acornelissen/Infidex_176_v_IDENTIDEM_design_remix/flocking/dxf/chamber-bottom.dxf

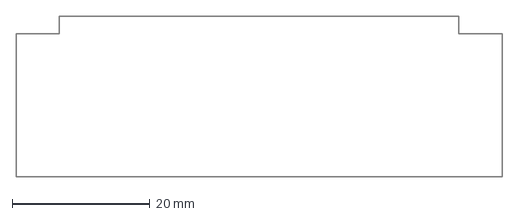
[picture p26: CAD file, 2026-09-22]
flocking/dxf/chamber-bottom.dxf
70.6 x 23.3 mm
