acornelissen/Infidex_176_v_IDENTIDEM_design_remix/3mf/parts/drag-cover.3mf

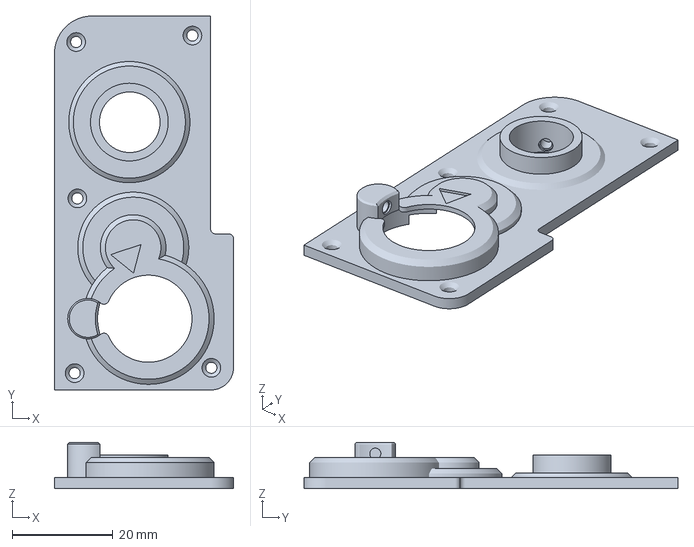
[picture p27: CAD file, 2026-09-30]
3mf/parts/drag-cover.3mf
35.5 x 74.1 x 9.20 mm
