acornelissen/Infidex_176_v_IDENTIDEM_design_remix/3mf/parts/advance-knob.3mf

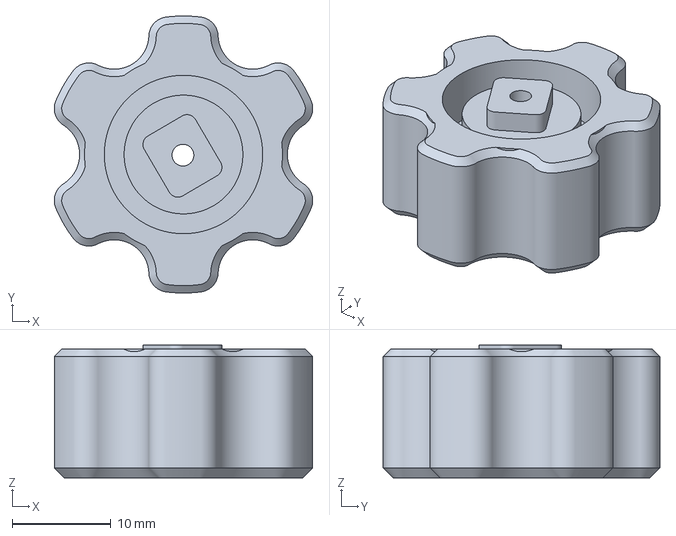
[picture p28: CAD file, 2026-09-28]
3mf/parts/advance-knob.3mf
26.1 x 28.0 x 13.4 mm
