acornelissen/Infidex_176_v_IDENTIDEM_design_remix/3mf/parts/rewind-knob.3mf

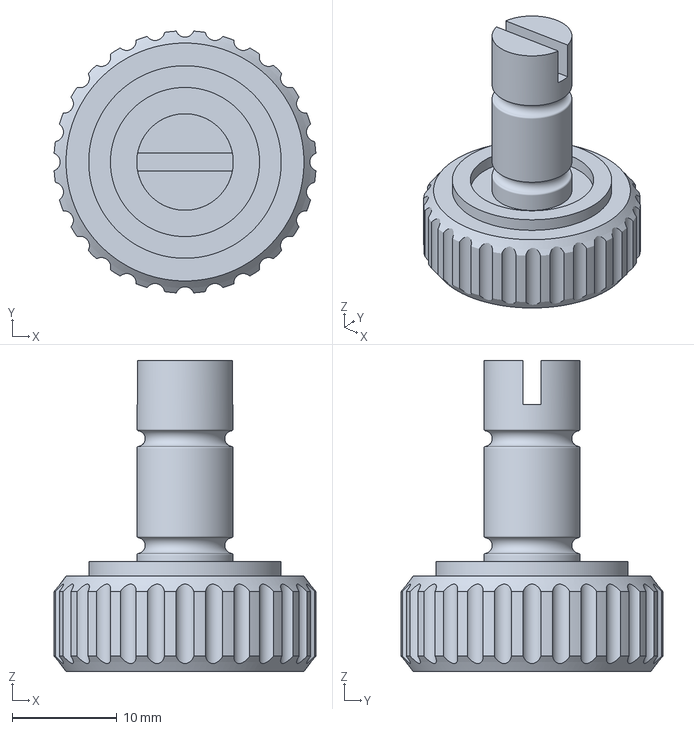
[picture p29: CAD file, 2026-09-28]
3mf/parts/rewind-knob.3mf
25.0 x 25.0 x 29.7 mm
