acornelissen/Infidex_176_v_IDENTIDEM_design_remix/3mf/parts/simple-cover.3mf

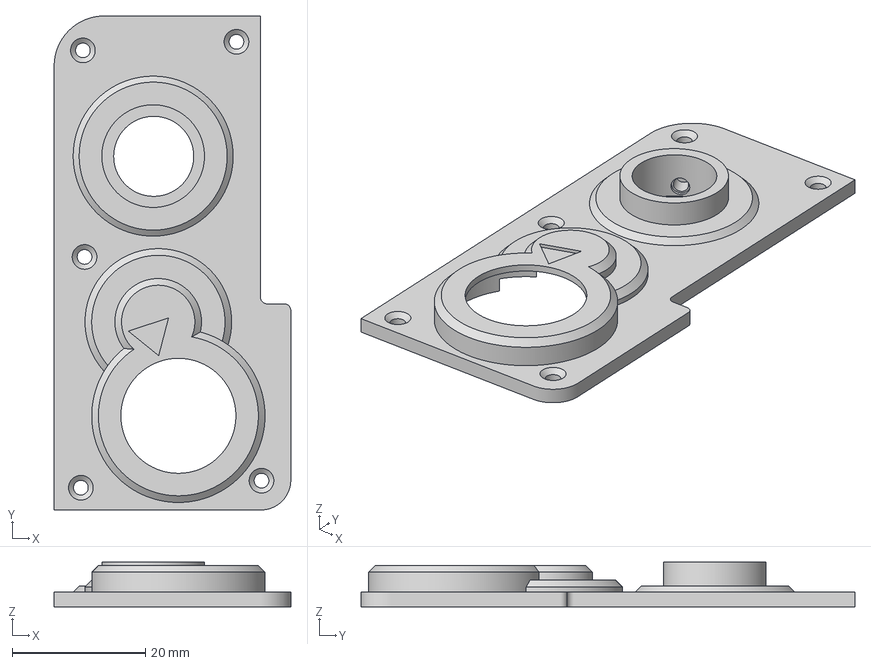
[picture p30: CAD file, 2026-09-28]
3mf/parts/simple-cover.3mf
35.5 x 74.1 x 6.70 mm
