acornelissen/Infidex_176_v_IDENTIDEM_design_remix/3mf/parts/counter-idler-1.3mf

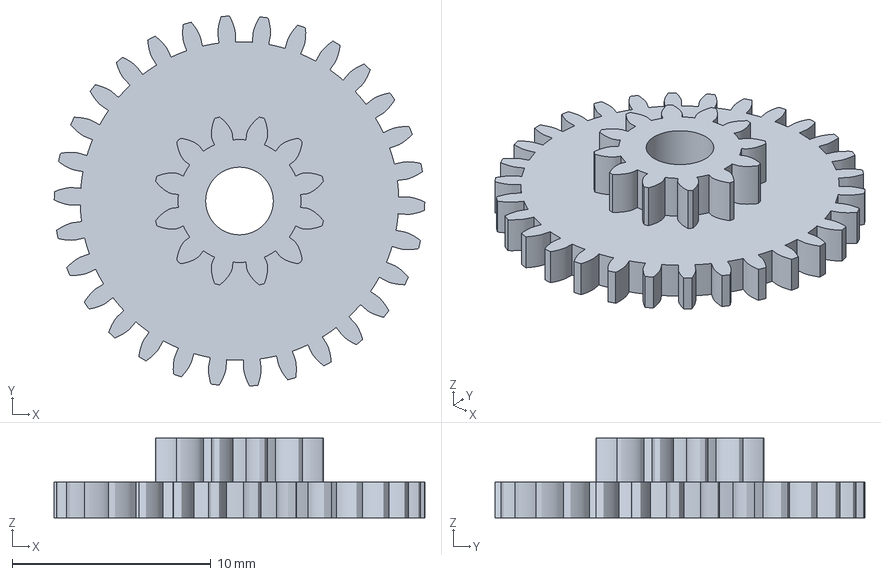
[picture p31: CAD file, 2026-09-27]
3mf/parts/counter-idler-1.3mf
18.6 x 18.6 x 4.00 mm
