acornelissen/Infidex_176_v_IDENTIDEM_design_remix/3mf/parts/counter-idler-2.3mf

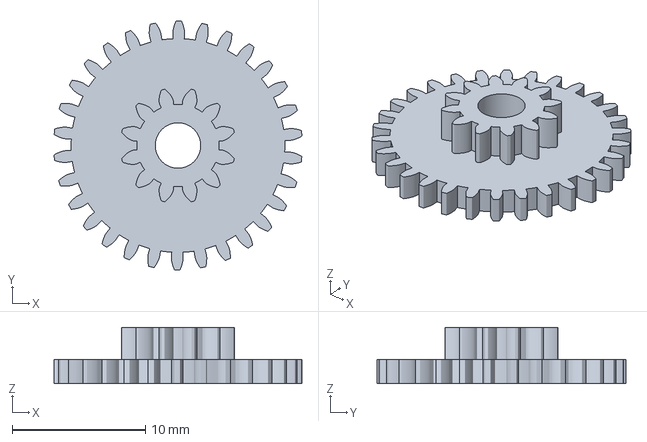
[picture p32: CAD file, 2026-09-27]
3mf/parts/counter-idler-2.3mf
18.6 x 18.6 x 4.20 mm
