acornelissen/Infidex_176_v_IDENTIDEM_design_remix/3mf/parts/counter-coupling-gear.3mf

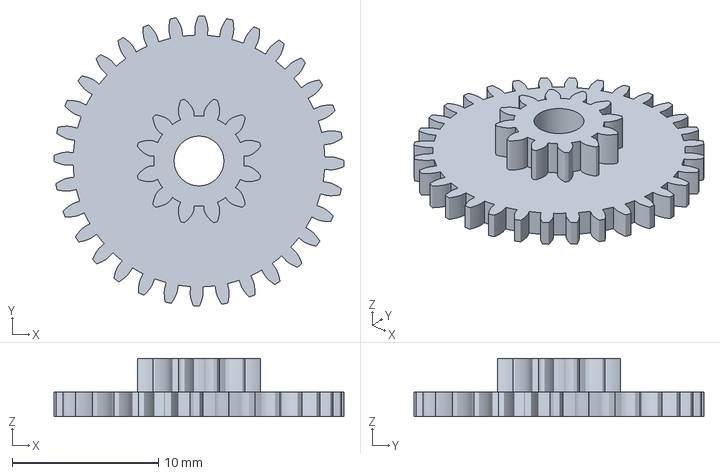
[picture p33: CAD file, 2026-09-27]
3mf/parts/counter-coupling-gear.3mf
19.8 x 19.8 x 4.00 mm
