acornelissen/Infidex_176_v_IDENTIDEM_design_remix/3mf/parts/body-solid.3mf

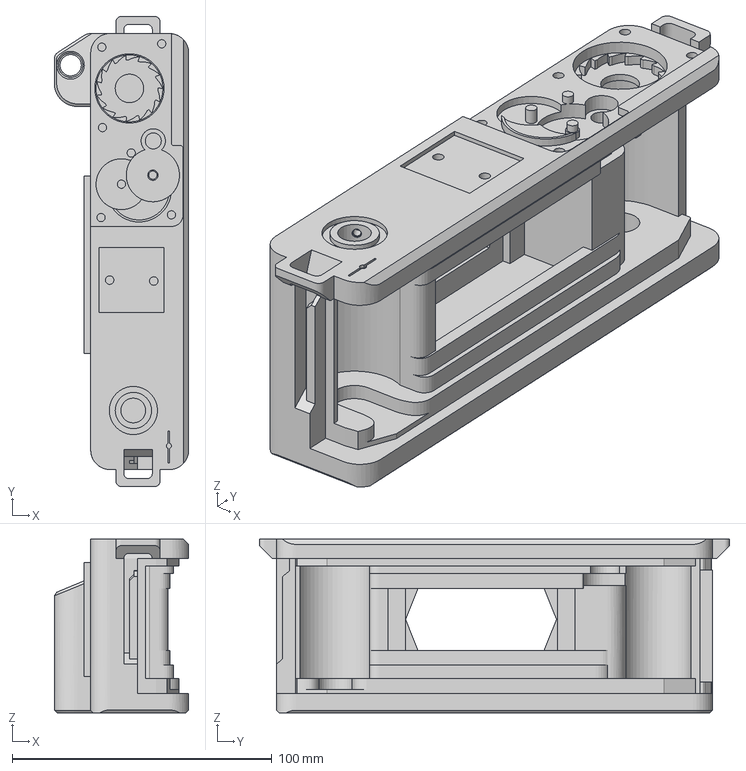
[picture p34: CAD file, 2026-09-26]
3mf/parts/body-solid.3mf
51.8 x 181.0 x 66.9 mm
