acornelissen/Infidex_176_v_IDENTIDEM_design_remix/3mf/parts/body-top.3mf

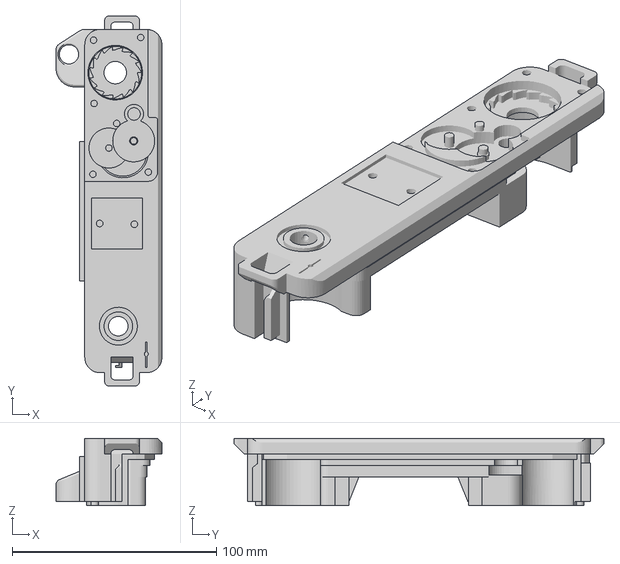
[picture p35: CAD file, 2026-09-26]
3mf/parts/body-top.3mf
51.8 x 181.0 x 32.8 mm
