acornelissen/Infidex_176_v_IDENTIDEM_design_remix/3mf/parts/sprocket.3mf

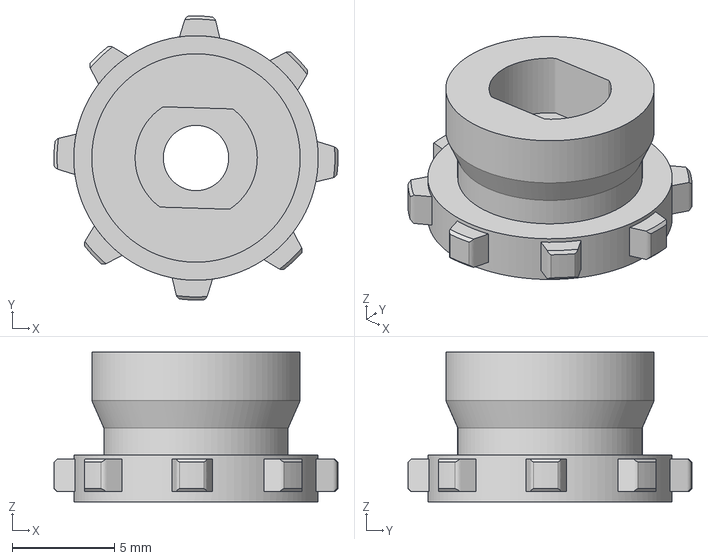
[picture p36: CAD file, 2026-09-25]
3mf/parts/sprocket.3mf
13.9 x 13.9 x 7.33 mm
