acornelissen/Infidex_176_v_IDENTIDEM_design_remix/3mf/parts/ratchet-coupling-gear.3mf

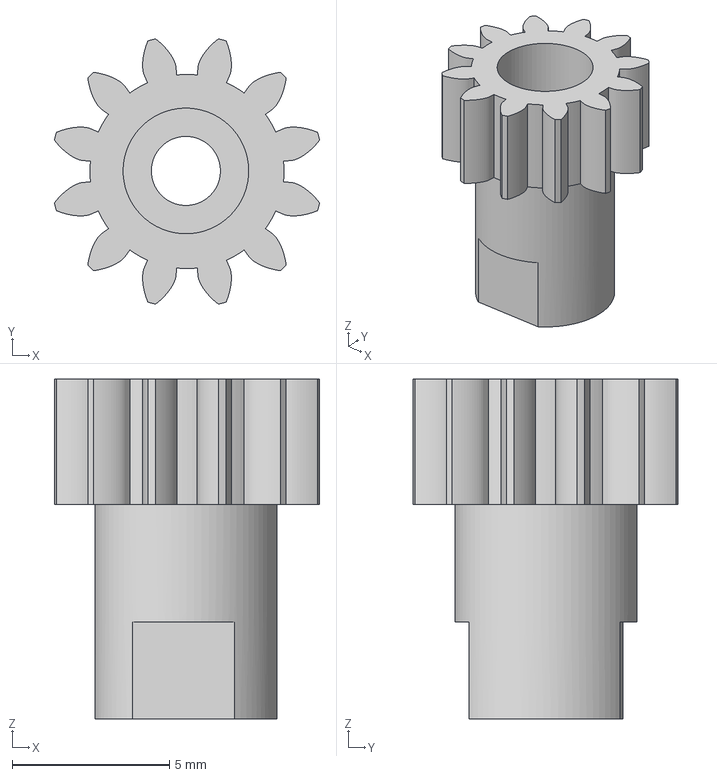
[picture p37: CAD file, 2026-09-25]
3mf/parts/ratchet-coupling-gear.3mf
8.45 x 8.45 x 10.8 mm
