acornelissen/Infidex_176_v_IDENTIDEM_design_remix/3mf/parts/body-bottom.3mf

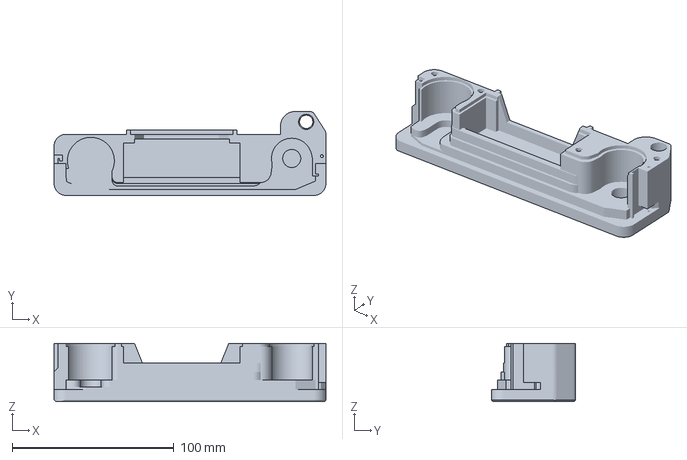
[picture p38: CAD file, 2026-09-24]
3mf/parts/body-bottom.3mf
168.0 x 51.8 x 36.1 mm
