acornelissen/Infidex_176_v_IDENTIDEM_design_remix/3mf/parts/door-var-1.3mf

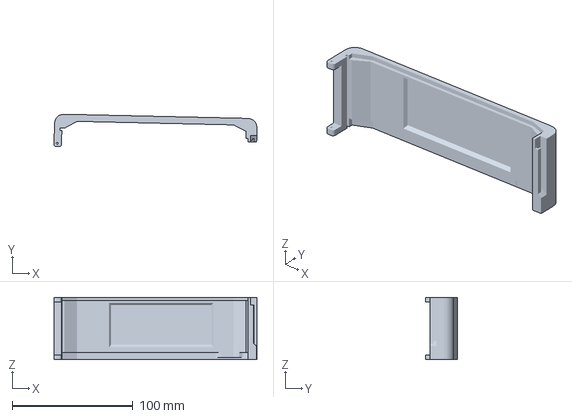
[picture p41: CAD file, 2026-09-18]
3mf/parts/door-var-1.3mf
168.3 x 26.9 x 51.7 mm
