acornelissen/Infidex_176_v_IDENTIDEM_design_remix/3mf/parts/door-var-2.3mf

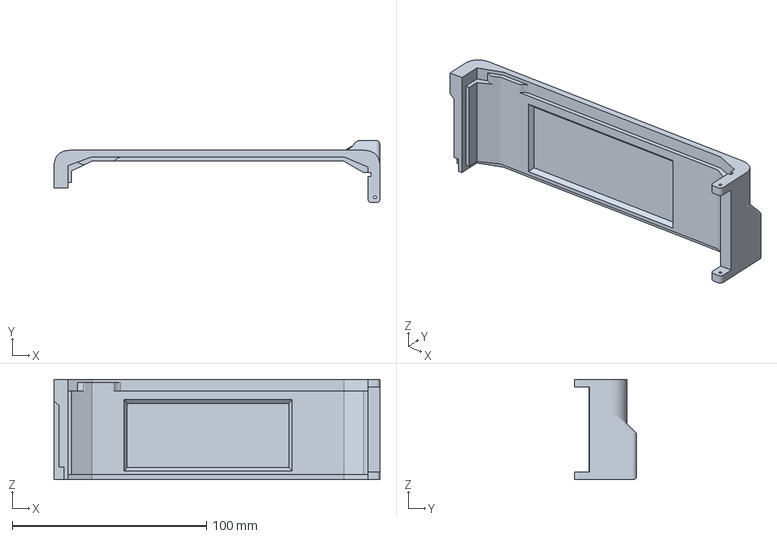
[picture p42: CAD file, 2026-09-18]
3mf/parts/door-var-2.3mf
168.0 x 32.1 x 51.7 mm
