acornelissen/Infidex_176_v_IDENTIDEM_design_remix/3mf/parts/helicoid-inner-ring-for-80mm-lens.3mf

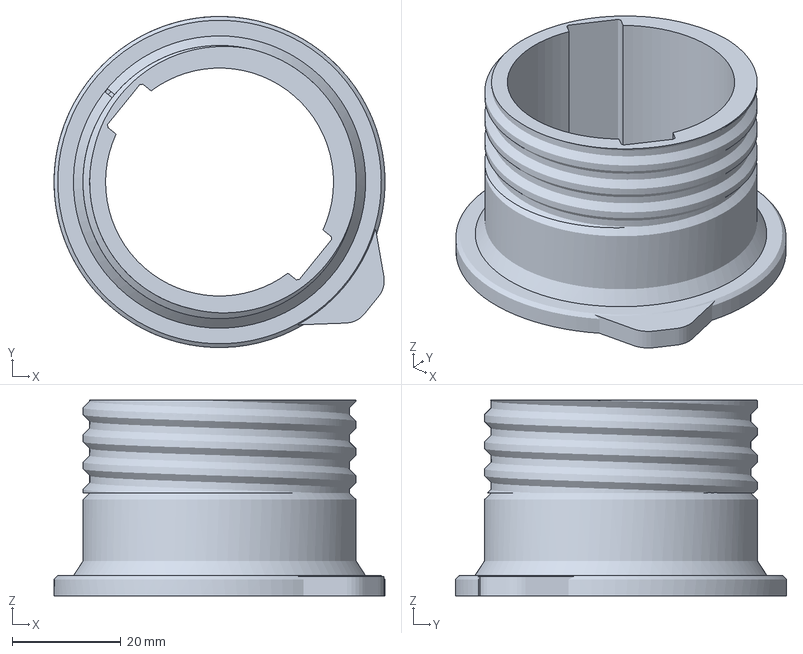
[picture p43: CAD file, 2026-09-18]
3mf/parts/helicoid-inner-ring-for-80mm-lens.3mf
61.0 x 61.0 x 36.1 mm
