acornelissen/Infidex_176_v_IDENTIDEM_design_remix/3mf/parts/latch.3mf

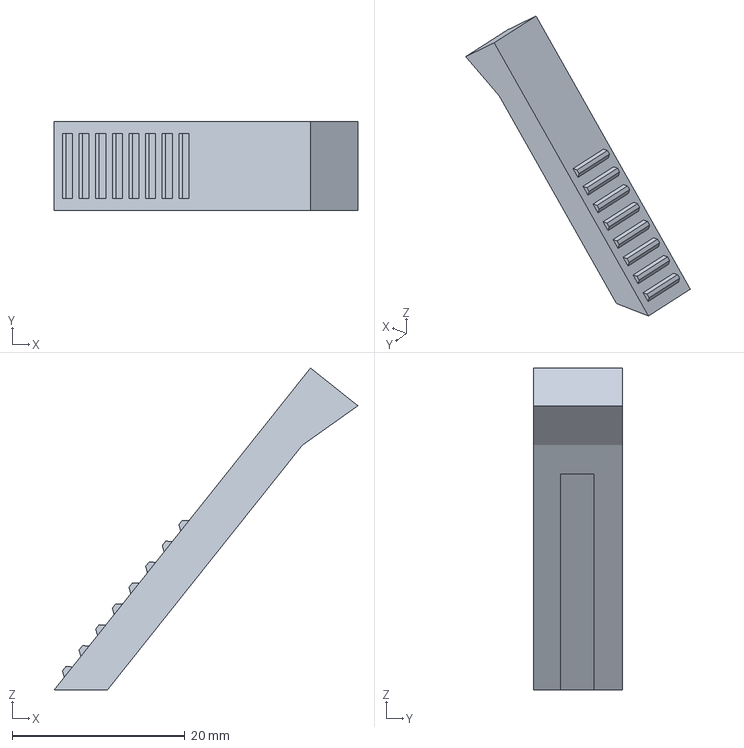
[picture p44: CAD file, 2026-09-18]
3mf/parts/latch.3mf
35.1 x 10.3 x 37.2 mm
