acornelissen/Infidex_176_v_IDENTIDEM_design_remix/3mf/parts/viewfinder-var-2.3mf

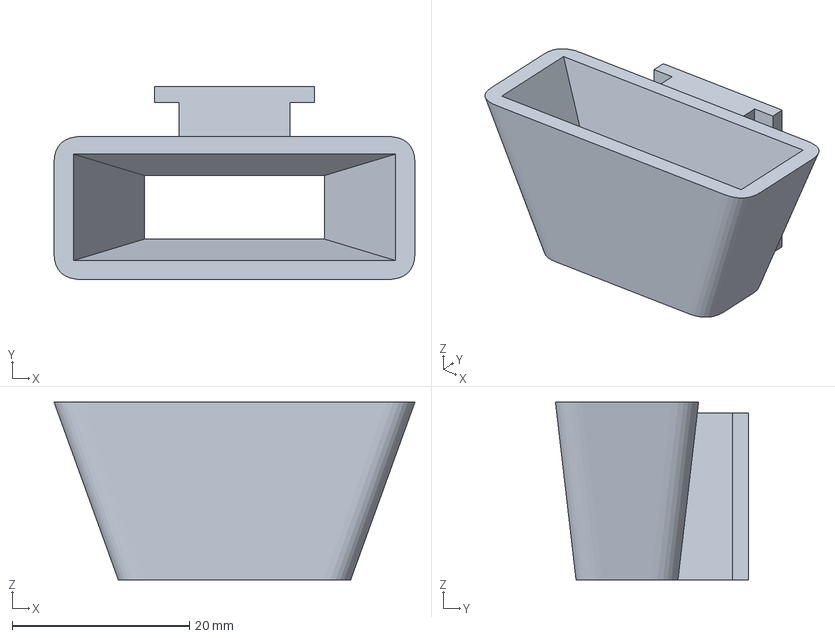
[picture p45: CAD file, 2026-09-18]
3mf/parts/viewfinder-var-2.3mf
40.7 x 21.8 x 20.1 mm
