acornelissen/Infidex_176_v_IDENTIDEM_design_remix/3mf/parts/pressure-plate-1.3mf

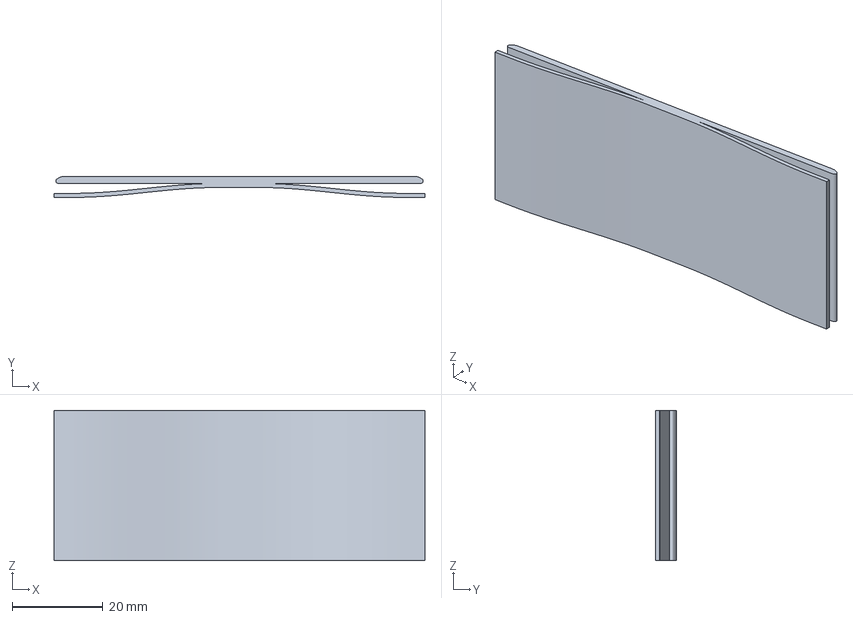
[picture p46: CAD file, 2026-09-18]
3mf/parts/pressure-plate-1.3mf
81.7 x 4.60 x 33.0 mm
