acornelissen/Infidex_176_v_IDENTIDEM_design_remix/3mf/parts/helicoid-focus-ring-no-ribs.3mf

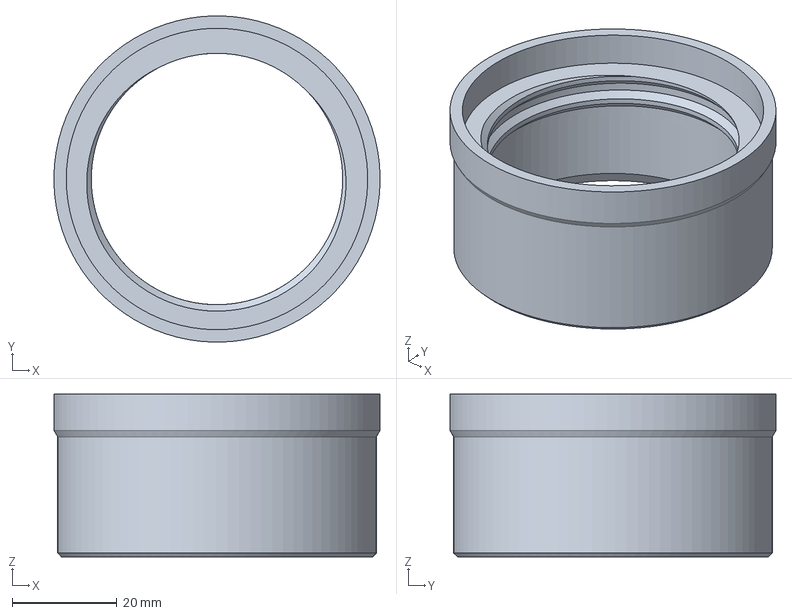
[picture p47: CAD file, 2026-09-18]
3mf/parts/helicoid-focus-ring-no-ribs.3mf
62.4 x 62.4 x 31.1 mm
