acornelissen/Infidex_176_v_IDENTIDEM_design_remix/3mf/parts/helicoid-lens-board.3mf

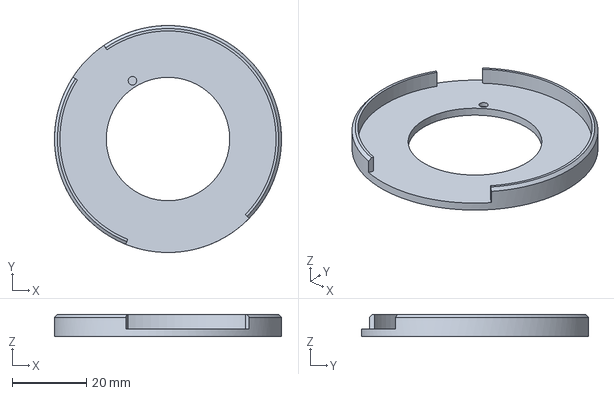
[picture p48: CAD file, 2026-09-18]
3mf/parts/helicoid-lens-board.3mf
61.0 x 61.0 x 6.00 mm
