acornelissen/Infidex_176_v_IDENTIDEM_design_remix/3mf/parts/inner-ratchet.3mf

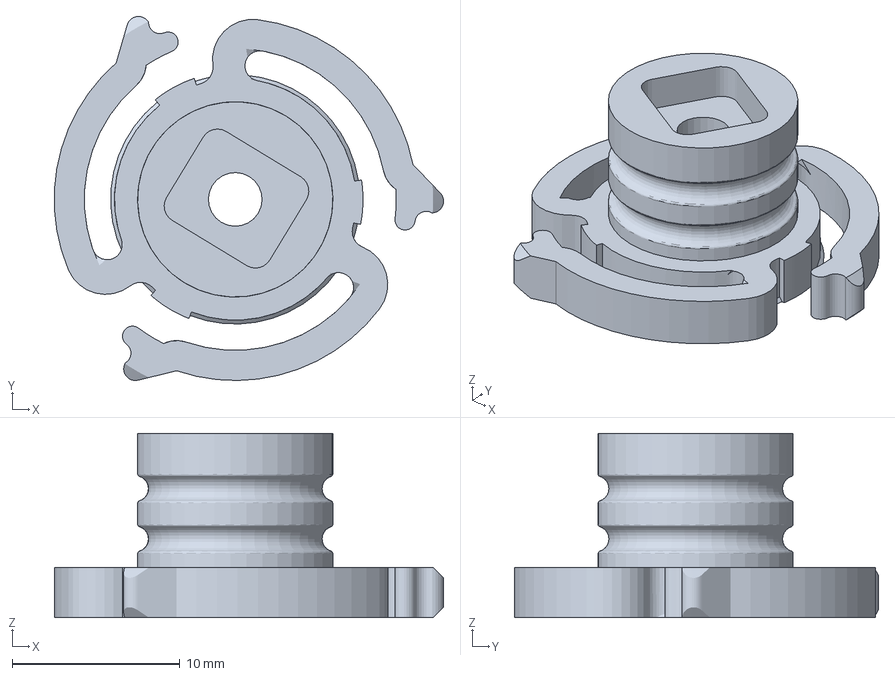
[picture p49: CAD file, 2026-09-18]
3mf/parts/inner-ratchet.3mf
23.2 x 21.7 x 11.0 mm
