acornelissen/Infidex_176_v_IDENTIDEM_design_remix/3mf/parts/helicoid-mount.3mf

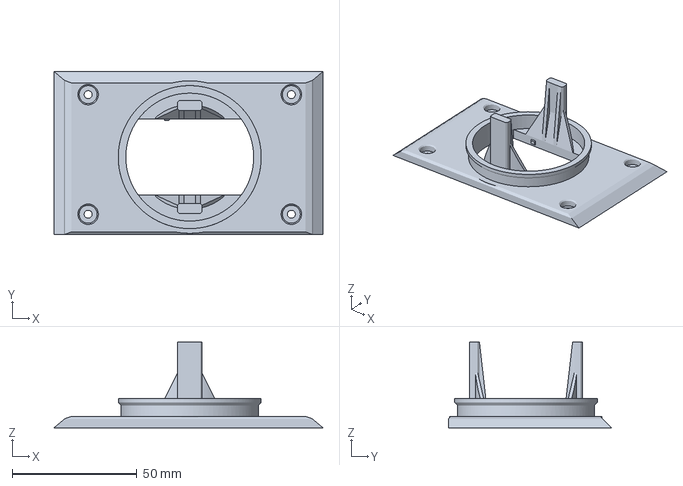
[picture p50: CAD file, 2026-09-18]
3mf/parts/helicoid-mount.3mf
107.6 x 65.2 x 34.2 mm
