acornelissen/Infidex_176_v_IDENTIDEM_design_remix/3mf/parts/door-var-4.3mf

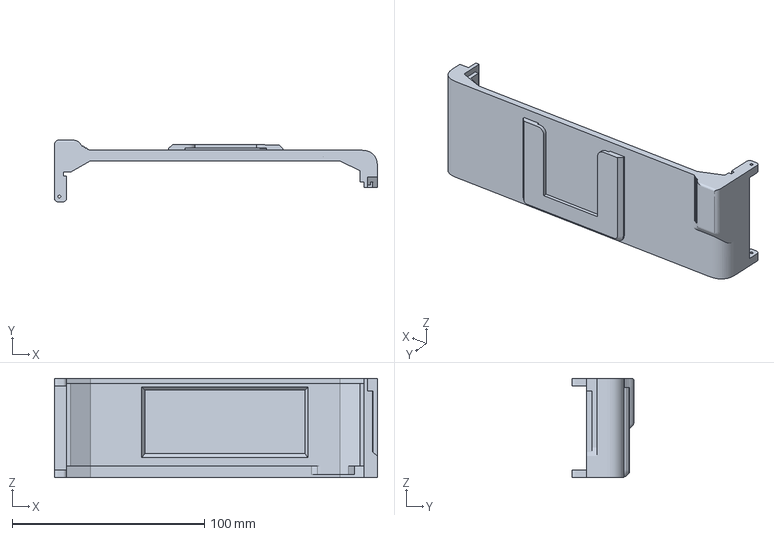
[picture p51: CAD file, 2026-09-18]
3mf/parts/door-var-4.3mf
168.0 x 32.1 x 51.7 mm
