acornelissen/Infidex_176_v_IDENTIDEM_design_remix/3mf/parts/helicoid-fix-ring.3mf

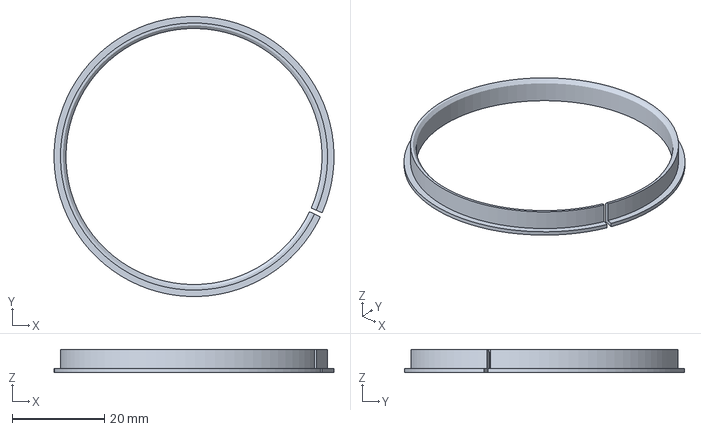
[picture p52: CAD file, 2026-09-18]
3mf/parts/helicoid-fix-ring.3mf
60.6 x 60.5 x 4.99 mm
