acornelissen/Infidex_176_v_IDENTIDEM_design_remix/3mf/parts/helicoid-inner-ring-for-55mm-lens.3mf

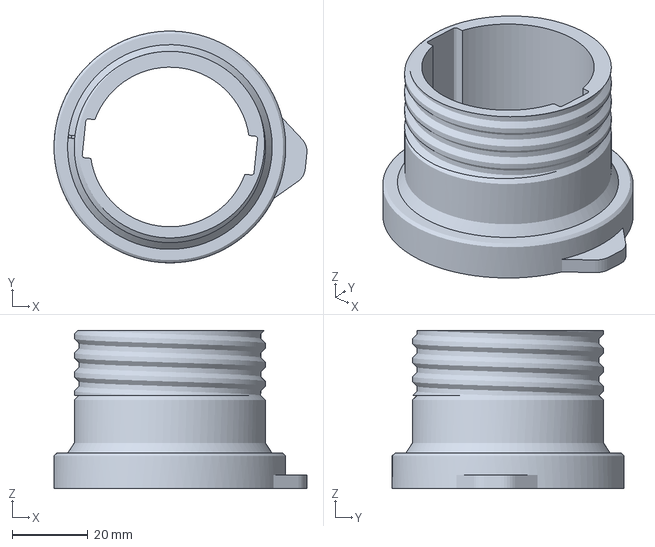
[picture p53: CAD file, 2026-09-18]
3mf/parts/helicoid-inner-ring-for-55mm-lens.3mf
66.6 x 61.0 x 41.7 mm
