acornelissen/Infidex_176_v_IDENTIDEM_design_remix/3mf/parts/take-up-spool.3mf

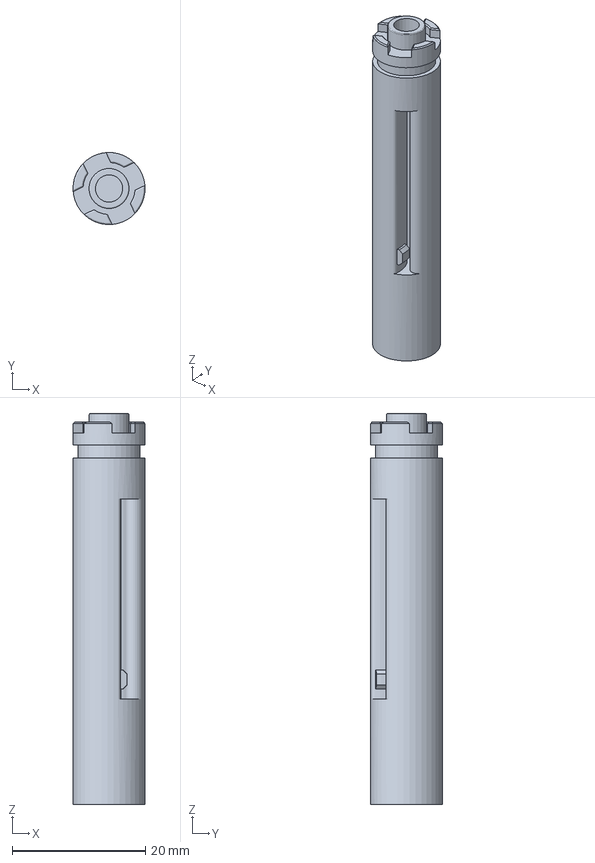
[picture p54: CAD file, 2026-09-18]
3mf/parts/take-up-spool.3mf
10.8 x 10.8 x 58.6 mm
