acornelissen/Infidex_176_v_IDENTIDEM_design_remix/3mf/parts/door-var-3.3mf

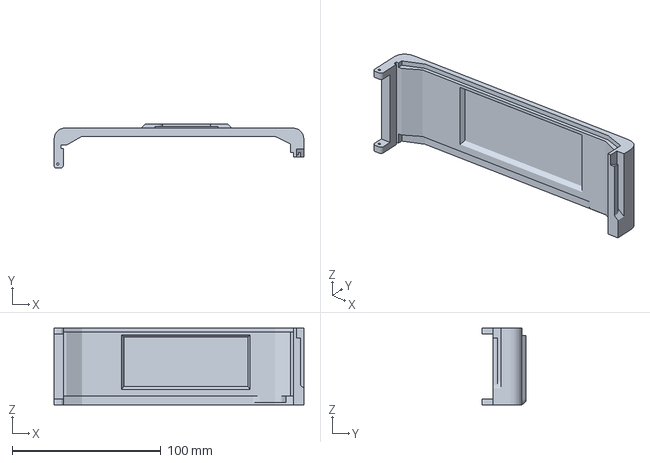
[picture p55: CAD file, 2026-09-18]
3mf/parts/door-var-3.3mf
168.0 x 29.8 x 51.7 mm
